sfnw-dev-owner/process-manuals/post-tilt-up/roof-framing-cklist.md

---
no-title-page: true
---

`#align(center,block[#set text(size:32pt); Post-Tilt-Up Checklist])`{=typst}

`#set text(size: 24pt);#v(3em)`{=typst}

- Attach White-Boards at Peak of Roof

- Align Rafters to Magic Studs

- Install Magic Stud Lag Bolts

- Secure Brackets at Peak of Roof

- Install Remaining Lag Bolts

- Install Bird Blocking

- Install Ridge Vent Blocks
