sfnw-dev-owner/process-manuals/Cut_Lists/Insulation.md

---
no-title-page: true
---

# INSULATION CUT LIST

## INTERIOR INSULATION

Cut and load in this order, back to front of the insulation cart, bottom level.

| Quantity | Dimensions | Notes |
| --- | --- | :--- |
| 12 | 24"x84" | Mark "Side Wall" |
| 2 | 24"x42" | Mark "Under Window" (2 pieces from one bat) |
| 1 | 24"x84" | Mark "Back Wall" |
| 1 | 24"x67½" | Mark "Under A/C" |
| 2 | 15½"x84" | Mark "Skinny" |

## EXTERIOR INSULATION

Cut and load in this order, back to front of the insulation cart, top level.

| Quantity | Dimensions | Notes |
| --- | --- | :--- |
| 8 | 24"x45½" | Mark "Middle Roof" (2 pieces from one bat) |
| 4 | 18"x45½" | Mark "End Roof" (2 pieces from one bat) |

Save some of the 12" cutoff pieces for use as insulation for
structural triangles; small pieces should be put into trash. There is a
black plastic bag for the saved insulation, next to the insulation
storage area.
