sfnw-dev-owner/process-manuals/Platform/Platform_sngl_side.md

```{=typst}
#title-page[
  #text(36pt, weight: "bold")[Platform]
  #v(1em)
  #text(24pt)[Jig Instructions]
]
```
# PLATFORM - SET UP LIST
- Put construction adhesive (Liquid Nails) by heater
- Caulking gun
- Framing nail gun
- Framing nails
- Screw gun with T25 bit
- Screws --- 3" with T25 head
- Screws --- hex head for brackets
- Brackets
- Chalk line
- Mallet
- Great Stuff cans
- 12" spacer blocks marked "SAVE"
- Jenga blocks

`#pagebreak()`{=typst}

# Step 1

- Set 2x6s into the jig to form the perimeter. Check the long 2x6s for straightness. If not straight, be sure to place them so that the curve
is inward at the center of each board. Put 1 FRAMING nail in each of the corners
    - one person holds flush on top and sides, other person nails
- Check the frame for square: measure the diagonals; they should be the same. Adjust as necessary.
- Put 2 more nails (total of 3) in a vertical line at each of the 4 corners.

`#pagebreak(); #fullpage("images/platform_01.pdf")`{=typst}

# Step 2
- Put a second 2x6 inside the ones on each short end
    - CLAMP them together
    - nail these 2x6 together 4 places at each end of frame, centered vertically
- Team leader
    - using the triangle, mark a line on the outside of the long 2x6s at the middle of the ends of each joist to show where the nails go.

`#pagebreak(); #fullpage("images/platform_02.pdf")`{=typst}

# Step 3
- Put in all the inner 2x6 joists
- Put 3 nails in a vertical line on each end of each joist
    - make sure joists are flush with side rail before nailing

`#pagebreak(); #fullpage("images/platform_03.pdf")`{=typst}

# Step 4

- Put pre-cut skids into the steel building carriages
    - longer part of the angled edges up
    - position each 4x6 skid so that the vertical mark on the skid lines up with the front of each carriage at the eventual front of the home.
- Install the alignment jigs, first to the front of the skids, and then to the back.
    - At the front, the cross bar should stick up above the tops of the  skids, and the two alignment blocks should be flush with the skid tops.
    - The skids should both be between the two alignment blocks.
- Place chocks under the wheels of one carriage, to keep if from moving.
- Measure diagonally from jig corner to corner and adjust the other carriage so that the jig is square.  Place chocks under its wheels.
- Pry the frame out of the framing jig, and lift the frame onto the pre-cut skids
    - At the front, the frame should be up against the alignment jig crossbar. At all four corners, the frame should fit into the metal angles.
    - Verify that the skids do not stick out beyond the back of the frame. If they do, they were not trimmed correctly, and this must be corrected.
- Measure the diagonals of the frame, and make sure that they are the same, so that the frame is square.
    - After any adjustments, **make sure** the frame is tight against the front jig crossbar.

`#pagebreak(); #fullpage("images/platform_04.pdf")`{=typst}

# Step 5

- Team Leader
    - make an X where the metal brackets should go
    - FOLLOW LOCATIONS on DIAGRAM
    - alternate inside of the skid and outside of the skid all the way to the rear
    - make sure to make a mark on the inside of the double joist at the rear.

`#pagebreak(); #fullpage("images/platform_05.pdf")`{=typst}

# Step 6
- At each X, screw in a metal bracket
    - use 6 small hexagonal screws for each metal bracket
    - 3 on the bottom 3 on the top, attaching the frame to the skids

`#pagebreak(); #fullpage("images/platform_06.pdf")`{=typst}

# Step 7

- Place blocks labeled "SAVE" in each bay, except the front and back bays
    - on top of each skid, centered between the joists.
    - DO NOT NAIL
    - In the front and back bays, place the "SAVE END" blocks

`#pagebreak(); #fullpage("images/platform_07.pdf")`{=typst}

# Step 8

- Put rigid insulation foam pieces into each bay
    - Cut the foam if not pre-cut. Use templates
    - 2 at 11^1^/~2~ inches wide by 92^1^/~2~ long
    - 7 at 14 inches wide by 92^1^/~2~ long
    - use an Exacto knife with blade all the way out
    - Cut the ends to fit the length, and install with silver side UP.
- Using GREAT STUFF spray cans
    - put lines to fill in at all the junctions between the foam and the joists.
    - Start with tip of spray can at the middle, and pull towards you.
    - DO NOT SET THE SPRAY CANS ON WORK STATIONS

`#pagebreak(); #fullpage("images/platform_08.pdf")`{=typst}

# Step 9
- Under the 1^st^ plywood panel ONLY
    - put Liquid Nails construction adhesive on each of the joists and along the side rails, only along the first 3 bays. 
- Place the 1^st^ plywood panel (3/4" CDX plywood)
    - use panels from pile labeled PLATFORM
    - line it up to be flush with the outer edges and the middle of the inner joist.
- Put a nail in that inner joist corner. Use that as the pivot point to line up the panel
- Nail about 8 inches apart along 2 edges using 3" framing nails.
- Put a chalk line at the intermediate joists
    - get up on platform and closely straddle the chalk line (joist) to push the plywood board down while nailing
    - walk backwards while nailing 8 inches apart.
- Nail along all chalk lines in a pattern going diagonally towards the opposite corner from where you started

`#pagebreak(); #fullpage("images/platform_09.pdf")`{=typst}

# Step 10

- Apply Liquid Nails construction adhesive to the joists that will be under the 2^nd^ plywood panel
- Place the 2^nd^ panel
    - at one side of the platform, put one nail into the 2^nd^ panel at the corner close to the 1^st^ panel
    - use this pivot point at the junction of the 2 panels to align the 2^nd^ panel
    - along the seam, nail about every 8 inches, slightly angled in towards the junction line
- Nail along edges and chalk lines

`#pagebreak(); #fullpage("images/platform_10.pdf")`{=typst}

# Step 11

- Apply Liquid Nails construction adhesive to the joists that will be under the 3^rd^ plywood panel
- Place the 3^rd^ panel
    - at one side of the platform, put one nail into the 3^rd^ panel at the corner close to the 2^nd^ panel
    - use pivot point at the junction of these panels to align the 3^rd^ panel
    - along the seam, nail about every 8 inches, slightly angled in towards the junction line
- Nail along edges and chalk lines

`#pagebreak(); #fullpage("images/platform_11.pdf")`{=typst}

# Step 12

- Router the edges of the platform. Ideally this would be done the next day, to let the liquid nails dry, but if tilt-up will be happening same-day, do it now.
  - Wipe off any liquid nails that's been squeezed out around the platform's perimeter.
  - Router the edges.
  - Clean the router's blade & table using an exacto knife and paper towel / rag. Try to leave all of the knife, router blade, and router table free of adhesive.

- Draw a line 3½ inches from the edge on all sides
    - use the marking jig; it hangs from the back saw table. Using a felt-tip pen, hold it against the inside of the jig,
    and slide the jig along the sides of the platform.

`#pagebreak(); #fullpage("images/platform_12.pdf")`{=typst}
