sfnw-dev-owner/process-manuals/Cut_Lists/Interior_Trim_Items.md

---
no-title-page: true
---

# Interior Trim Pick List

## Trim Racks -- West Wall

Trim widths (4" or 2") are approximate.  Do not rely on these dimensions.

| Qty | Size | Length | Description |
| :--- | :--- | :--- | --- |
|  3 | 3/4 x 4 | 12 ft | PVC Baseboards |
| 16 | 1/2 x 2 | 96" | Long Trim |
|  6 | 1/2 x 2 | 44" or 48"| Short Trim |
|  5 | 1/2 x 2 | 38" | Window Opening Trim |
|  6 | 1/2 x 3-1/8 | 35" | Window Liner |
|  6 | 1/2 x 2 | 42" | Ceiling Seam Trim |
|  2 | 1/2 x 2 | 42" | Triangle Trim -- Left |
|  2 | 1/2 x 2 | 42" | Triangle Trim -- Right |
|  2 | 1/2 x 2 | 12" | Triangle Trim -- Center  (use scraps)|
|  1 | 1/2 x 9-1/2| 96" | Wide Trim -- Front Door |

## Window Shelves -- near Band Saw

| Qty | Size | Length | Description |
| :--- | :--- | :--- | --- |
| 1 | 3/4 x 8 | 40" | Rear Shelf |
| 1 | 3/4 x 8 | 40" | Front Shelf |
| 1 | 2 x 4 | 39" | Rear Support Block |
| 1 | 2 x 4 | 39-1/2" | Front Support Block |

## Vent Cap (on Trim Rack)

| Qty | Size | Length | Description |
| :--- | :--- | :--- | --- |
| 1 | 1/2 x 9-1/2 | 96" | Wide Trim |
| 1 | 1/2 x 9-1/2 | ~44" | Wide Trim |
| 4 | 2 x 4 | 6-1/2" | Vent Block |

### Notes

- Verify width between finished window liner and midpoint of door frame, and rip 9-1/2 plank to this width.  Remaining strip can be used behind the door.
- Match plank widths of Wide Trim for Vent Cap, so that the seam will be less obvious
- Cut 13" blocks under front chop saw in half for Vent Blocks
