sfnw-dev-owner/process-manuals/Extract_Iron_Carts/images/01_Prepare.pdf

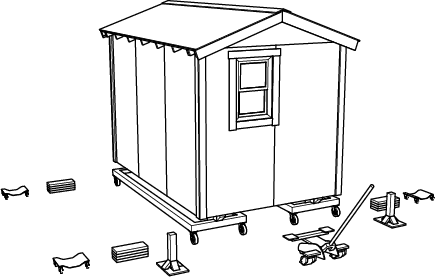
[picture p63: page 1]
