sfnw-dev-owner/process-manuals/Platform/archived/README.md

The files in this directory were used in Oct/Nov 2025 while building
for Eagle Village for Chief Seattle Club. They describe how to build a
platform with doubled side rails (2x6x12'), which we don't do anymore.
