sfnw-dev-owner/process-manuals/Platform/archived/images/platform_v2_01.pdf

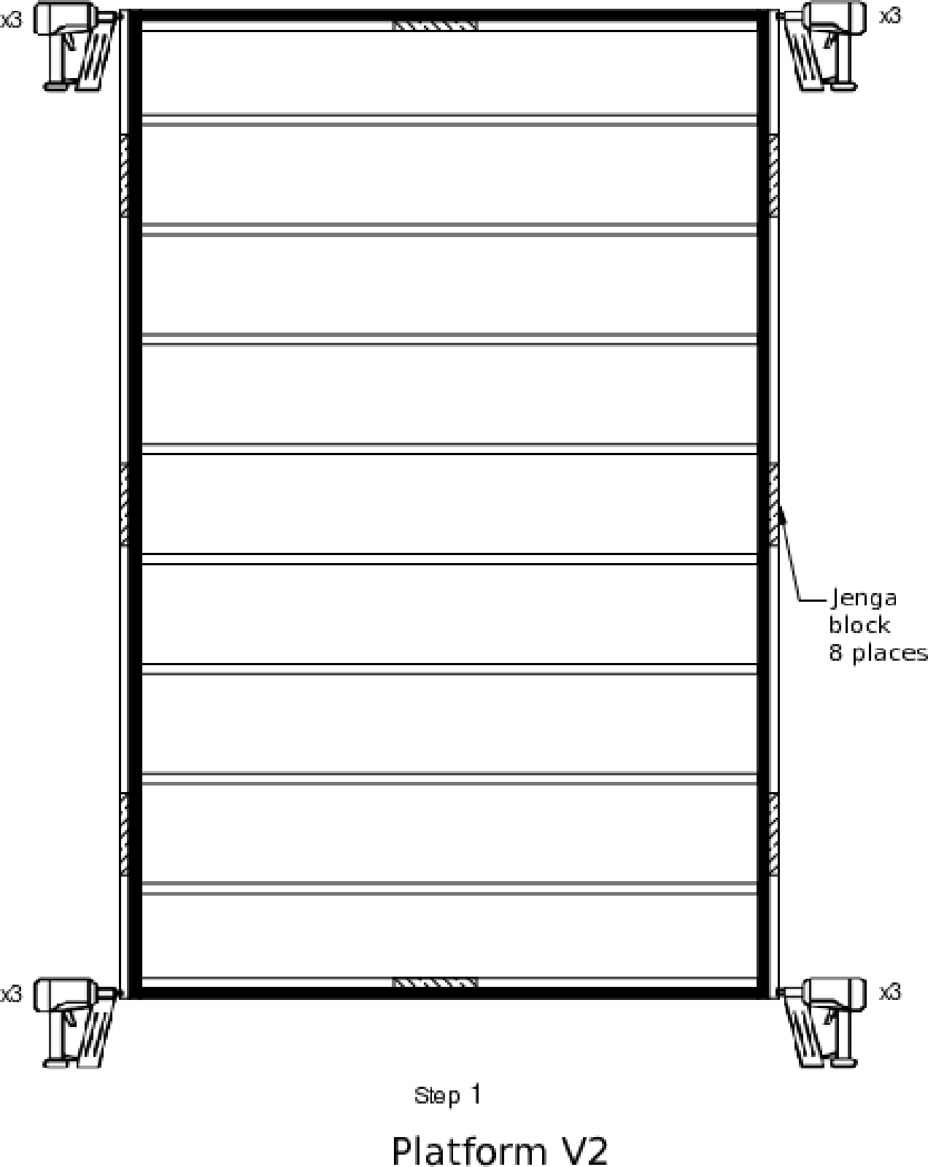
[picture p64: page 1]
