sfnw-dev-owner/process-manuals/Platform/archived/images/platform_v2_02.pdf

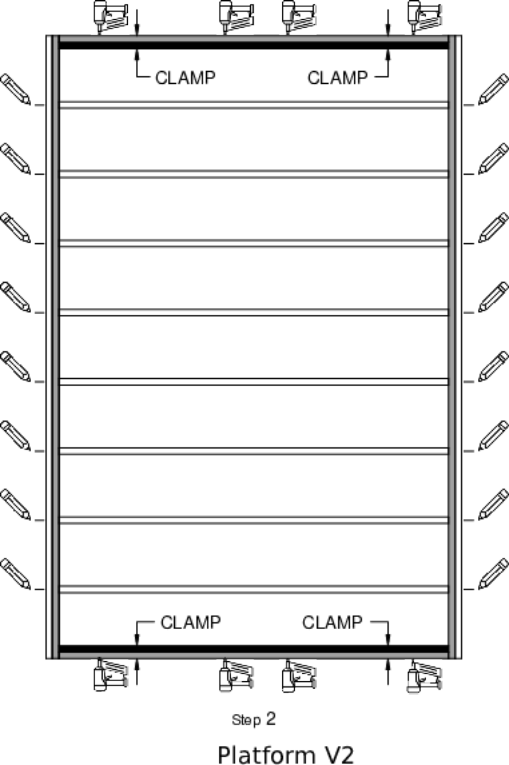
[picture p65: page 1]
