sfnw-dev-owner/process-manuals/Platform/archived/images/platform_v2_03.pdf

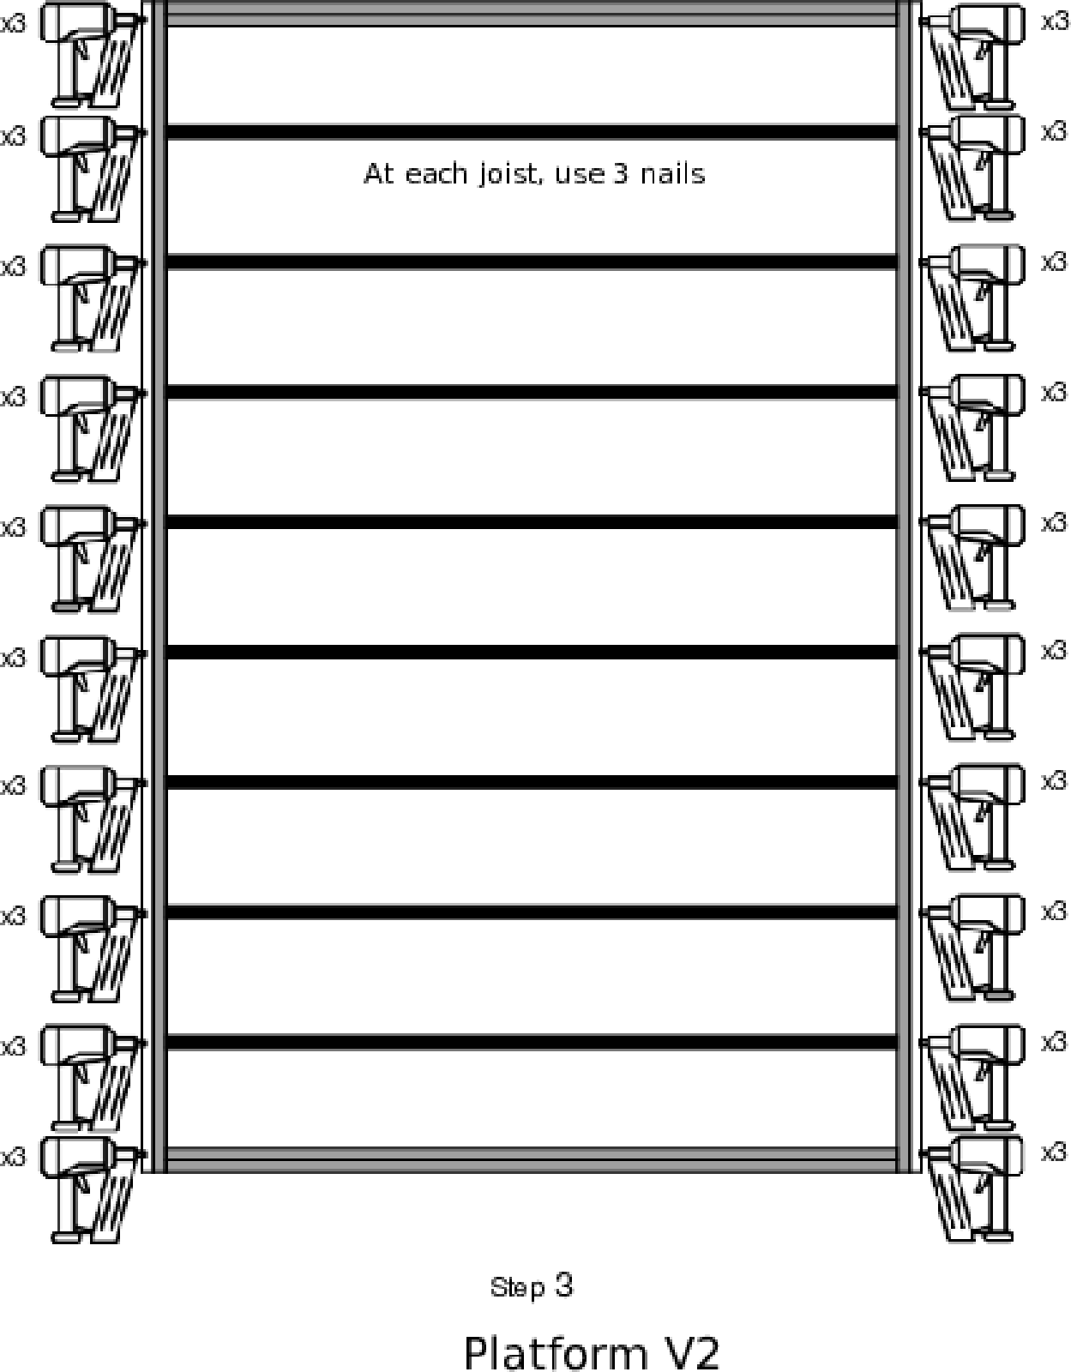
[picture p66: page 1]
