sfnw-dev-owner/process-manuals/Platform/archived/images/platform_v2_04.pdf

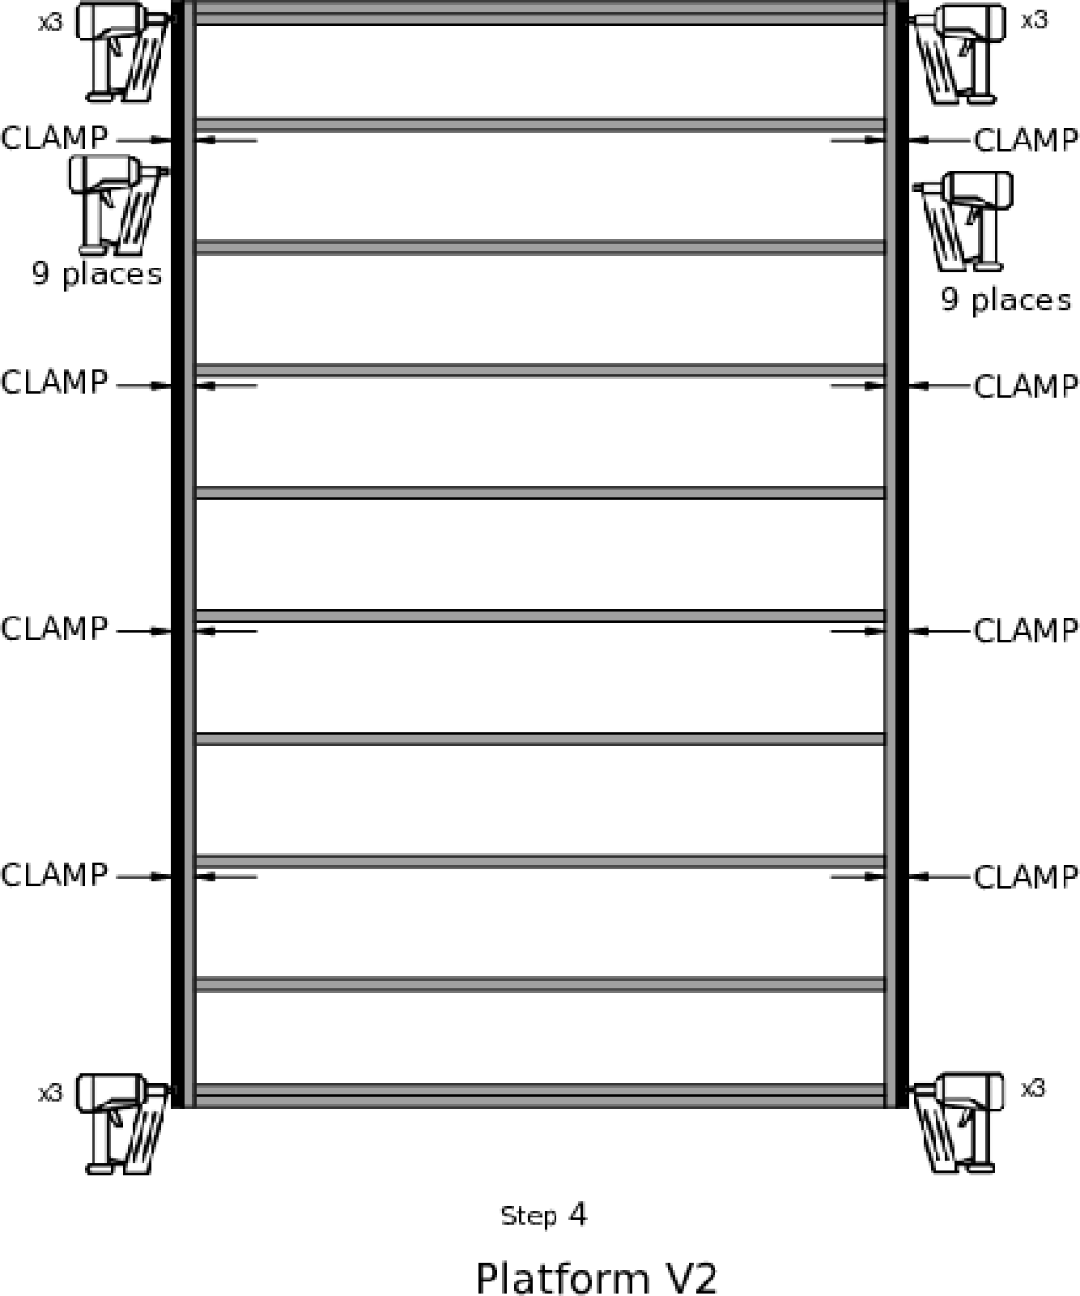
[picture p67: page 1]
