sfnw-dev-owner/process-manuals/Platform/archived/images/platform_v2_05.pdf

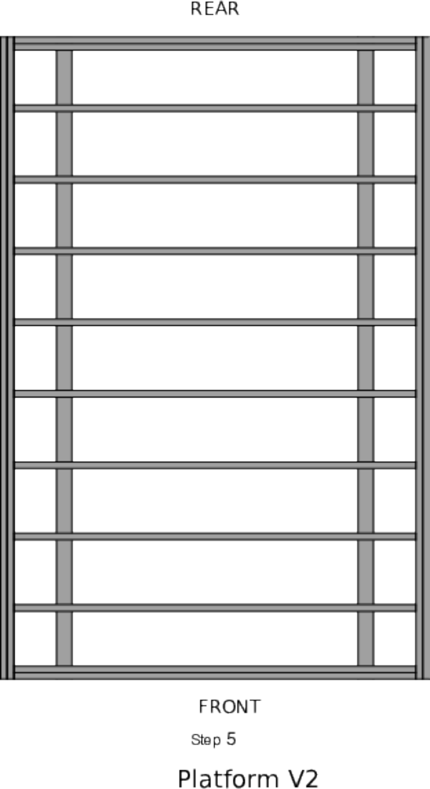
[picture p68: page 1]
