sfnw-dev-owner/process-manuals/Platform/archived/images/platform_v2_06.pdf

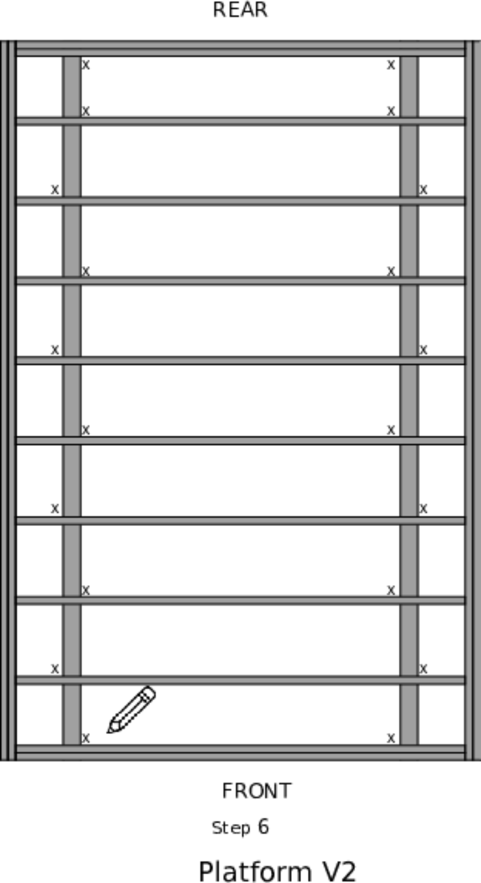
[picture p69: page 1]
