sfnw-dev-owner/process-manuals/Platform/archived/images/platform_v2_07.pdf

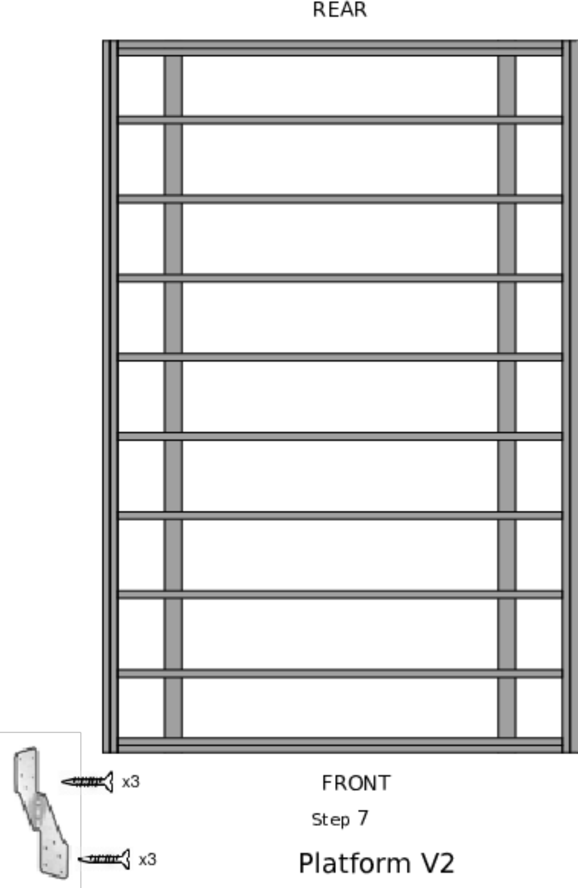
[picture p70: page 1]
