sfnw-dev-owner/process-manuals/Platform/archived/images/platform_v2_08.pdf

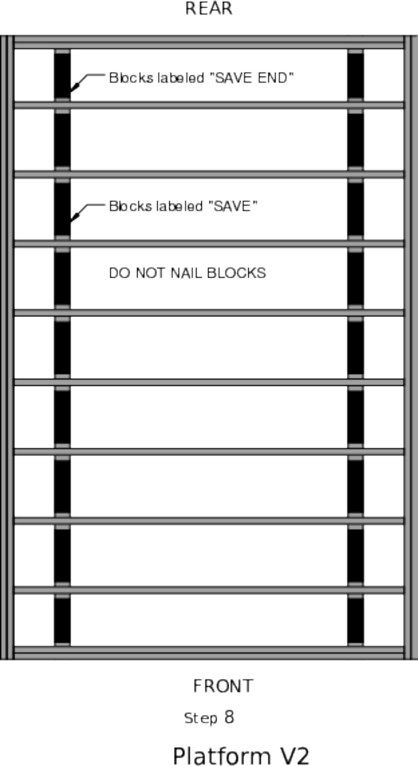
[picture p71: page 1]
