sfnw-dev-owner/process-manuals/Platform/archived/images/platform_v2_09.pdf

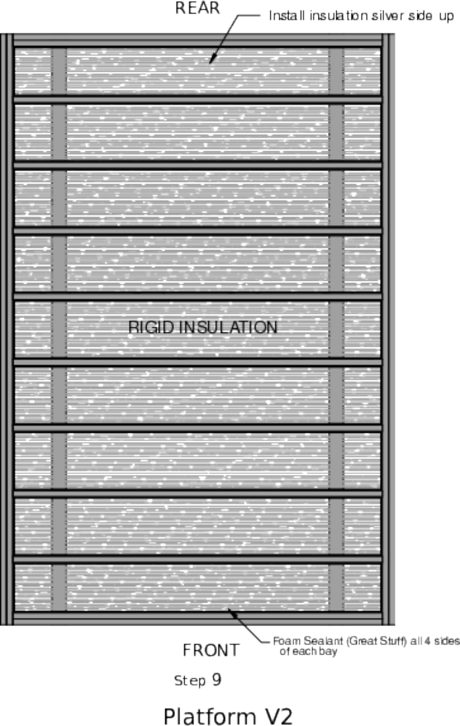
[picture p72: page 1]
