sfnw-dev-owner/process-manuals/Platform/archived/images/platform_v2_10.pdf

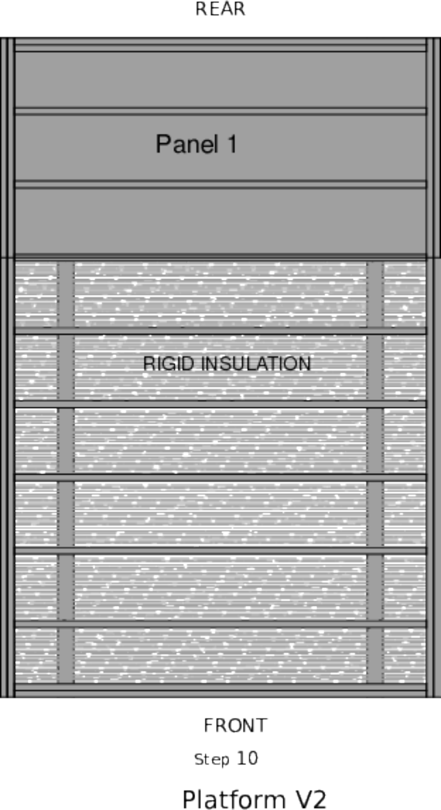
[picture p73: page 1]
