sfnw-dev-owner/process-manuals/Platform/archived/images/platform_v2_11.pdf

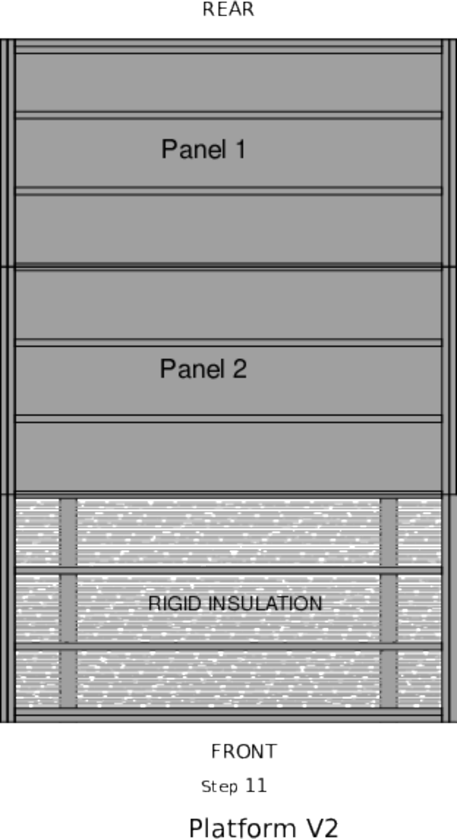
[picture p74: page 1]
