sfnw-dev-owner/process-manuals/Platform/archived/images/platform_v2_12.pdf

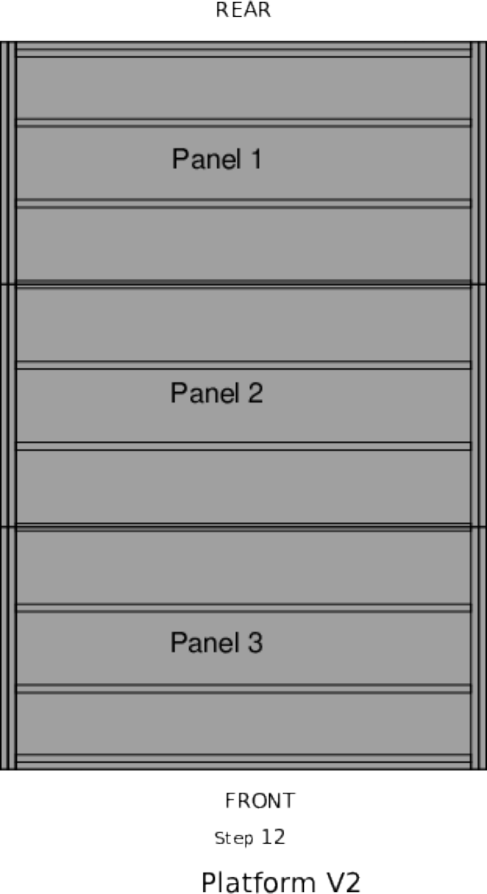
[picture p75: page 1]
