sfnw-dev-owner/process-manuals/Platform/archived/images/platform_v2_13.pdf

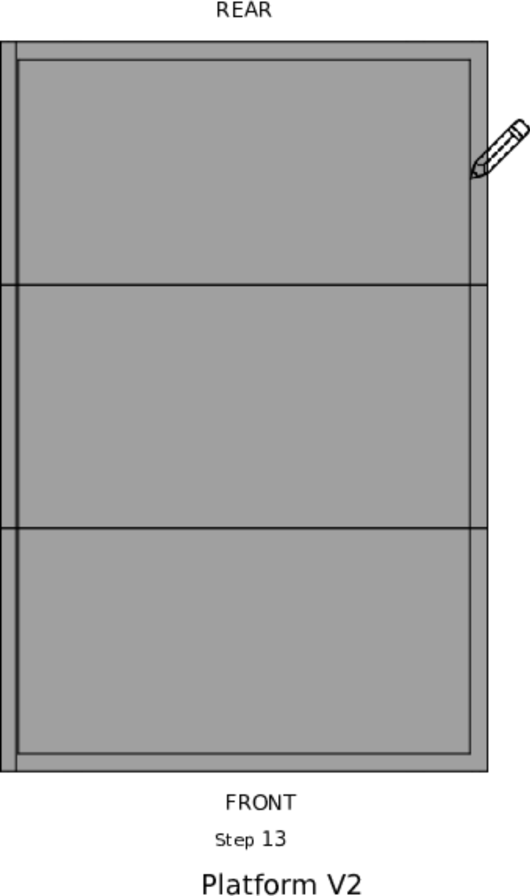
[picture p76: page 1]
