sfnw-dev-owner/process-manuals/post-tilt-up/images/image_44.png

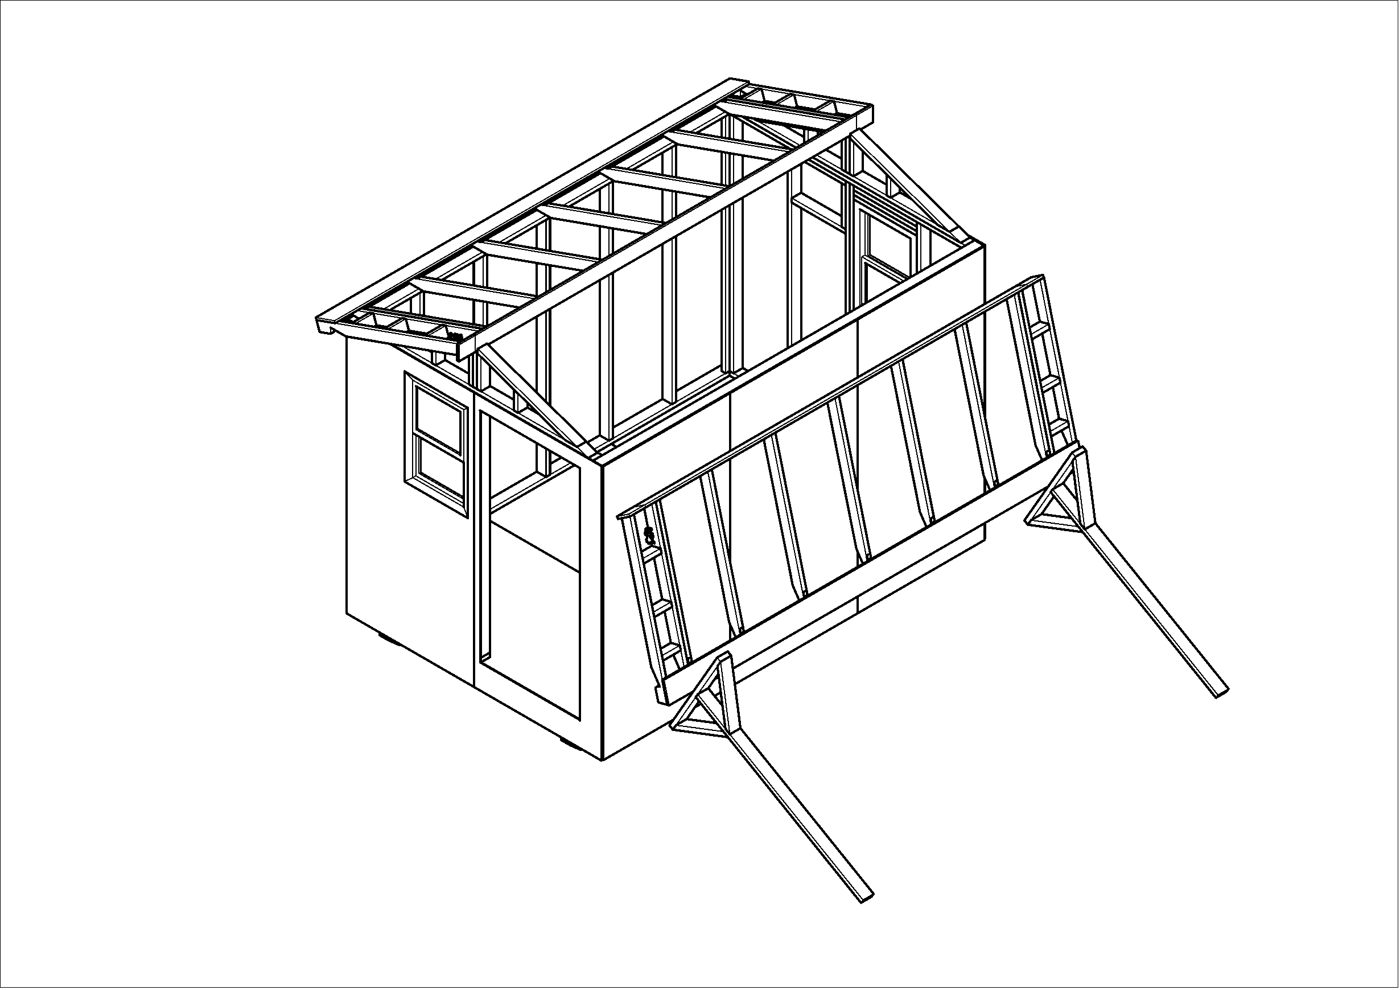
post-tilt-up/images/image_44.png
