sfnw-dev-owner/process-manuals/tilt-up/images/image_04.png

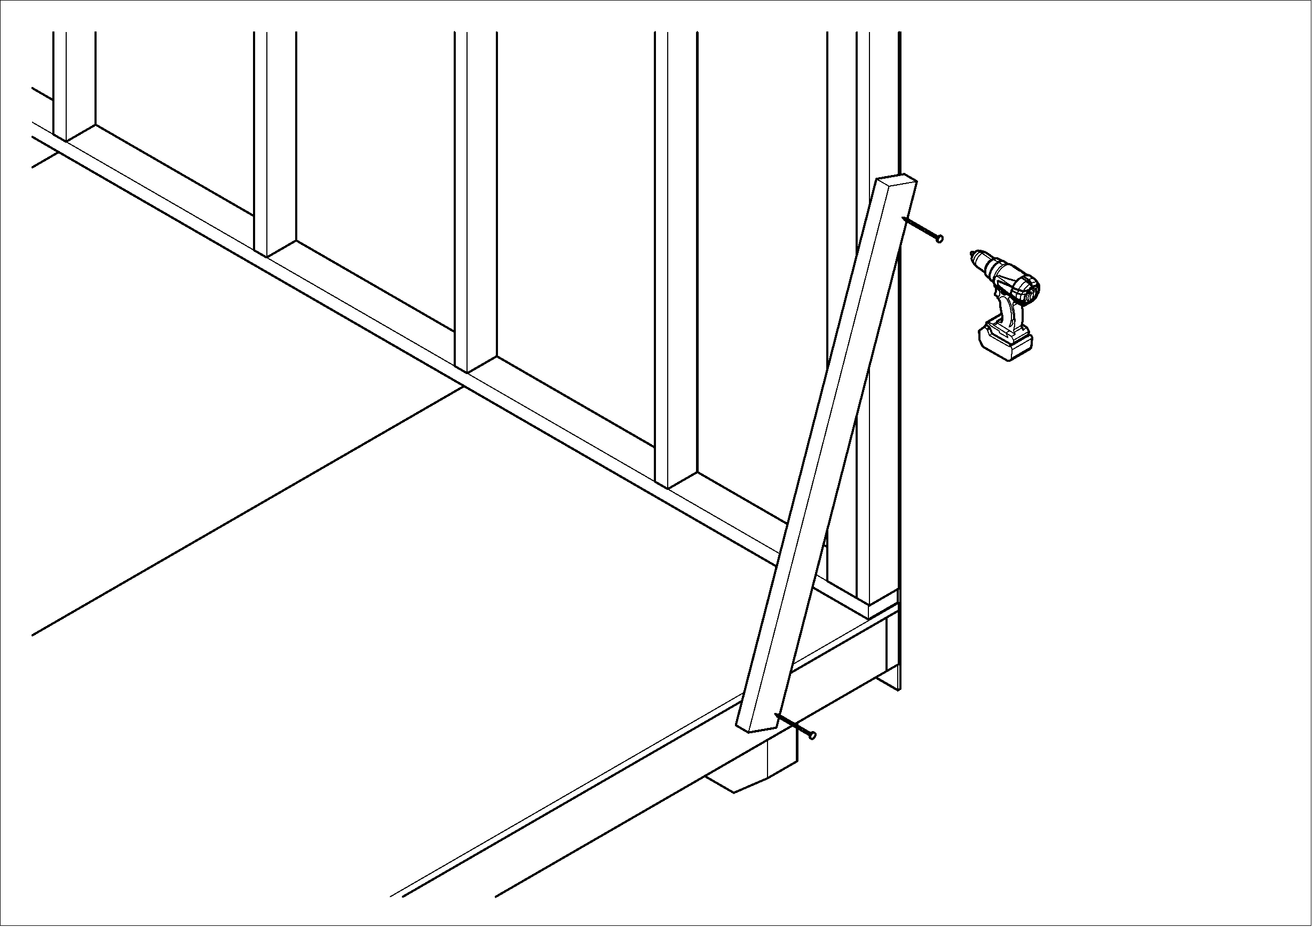
tilt-up/images/image_04.png
