sfnw-dev-owner/process-manuals/tilt-up/images/image_07.png

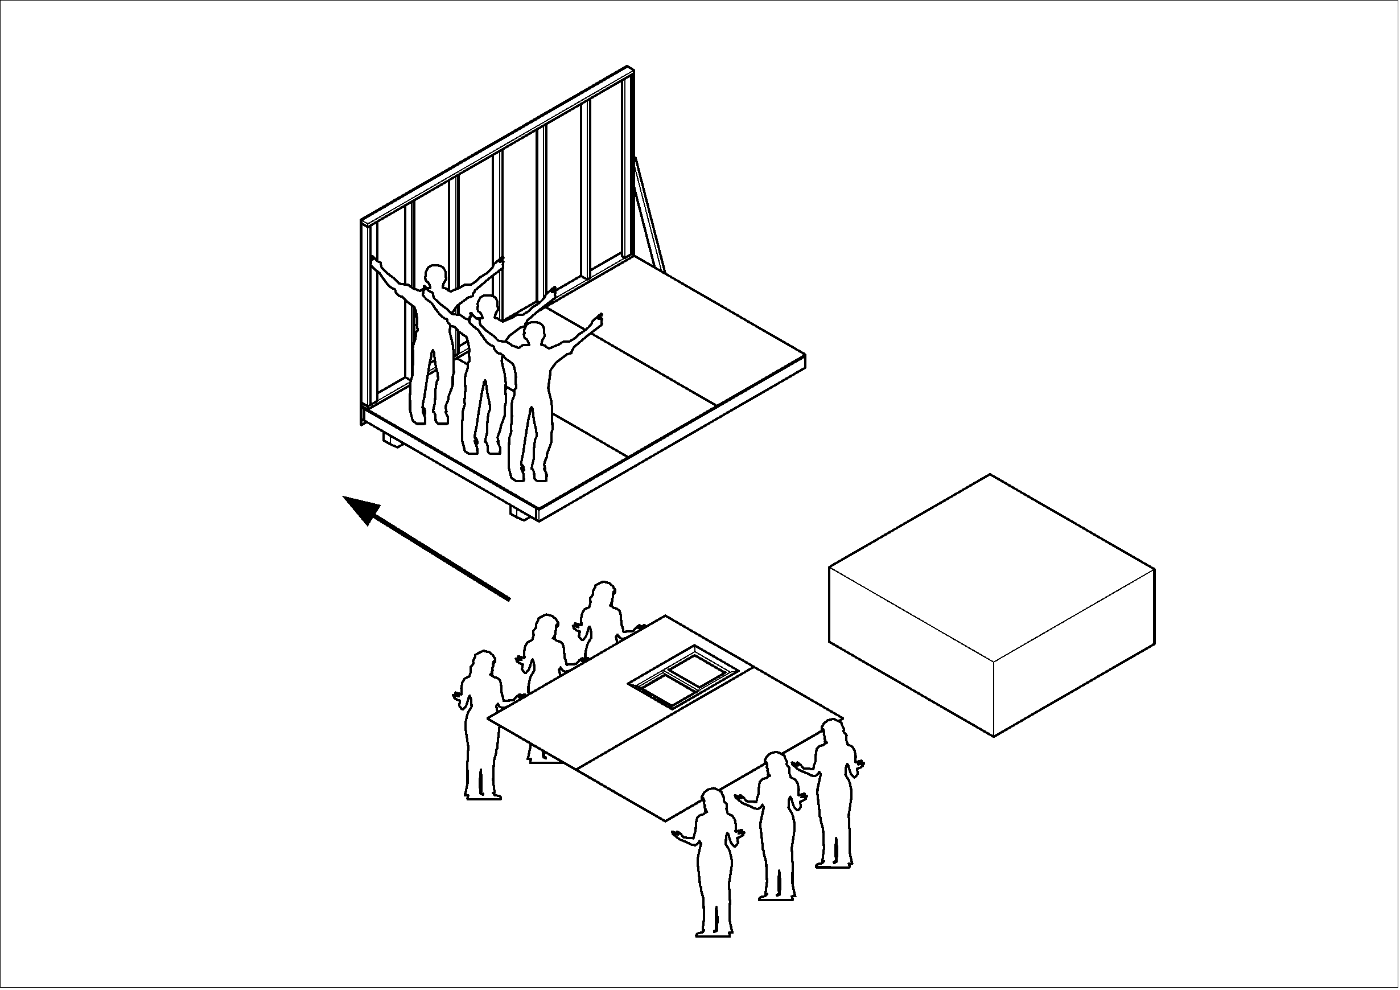
tilt-up/images/image_07.png
