sfnw-dev-owner/process-manuals/tilt-up/images/image_08.png

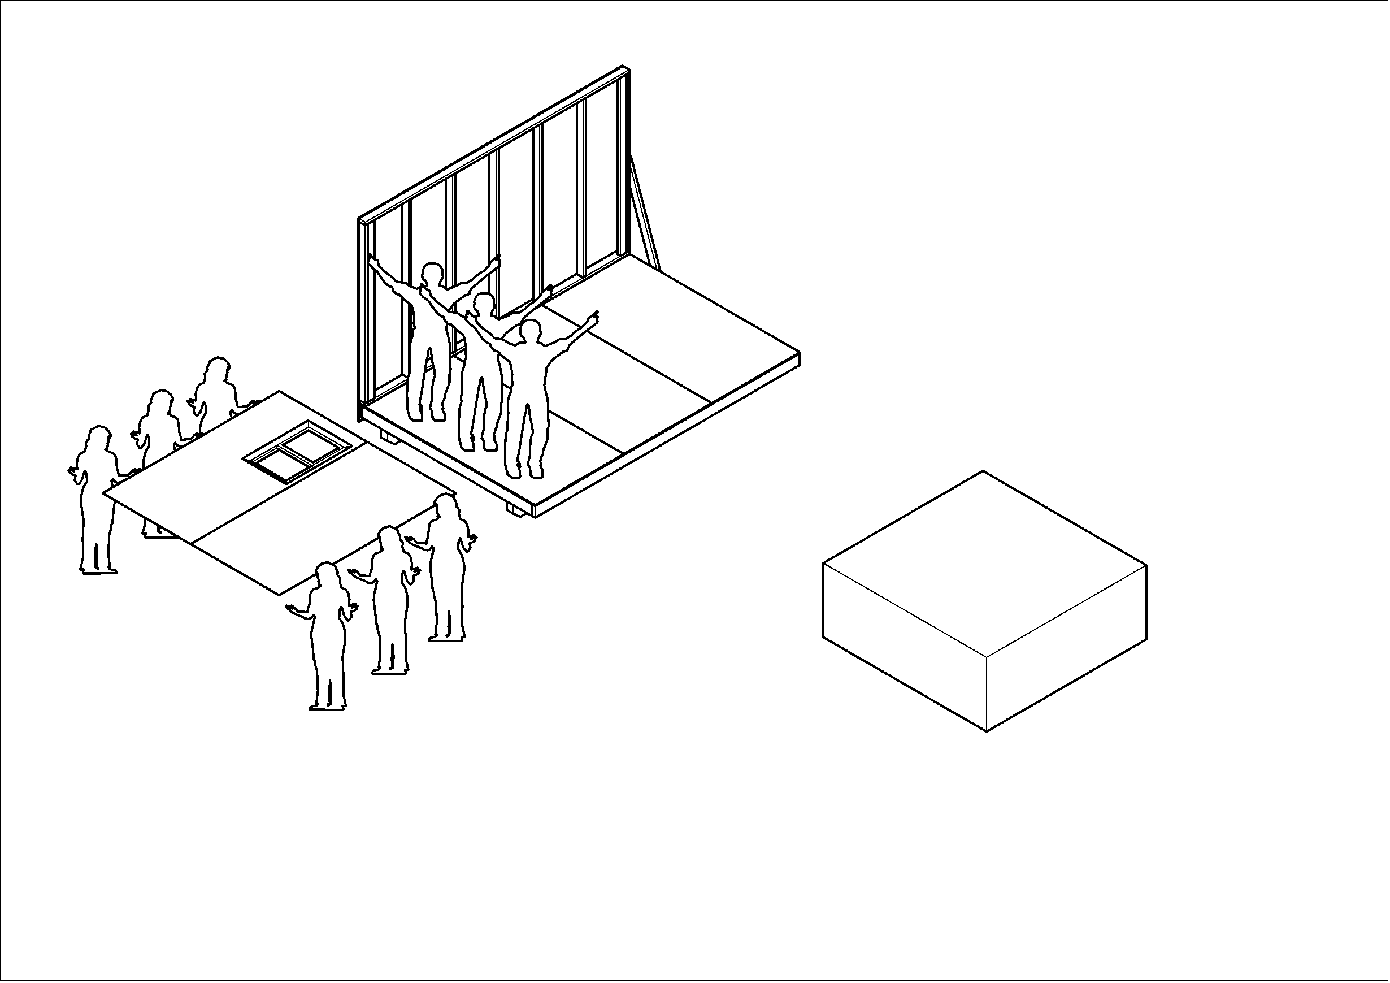
tilt-up/images/image_08.png
