sfnw-dev-owner/process-manuals/tilt-up/images/image_10.png

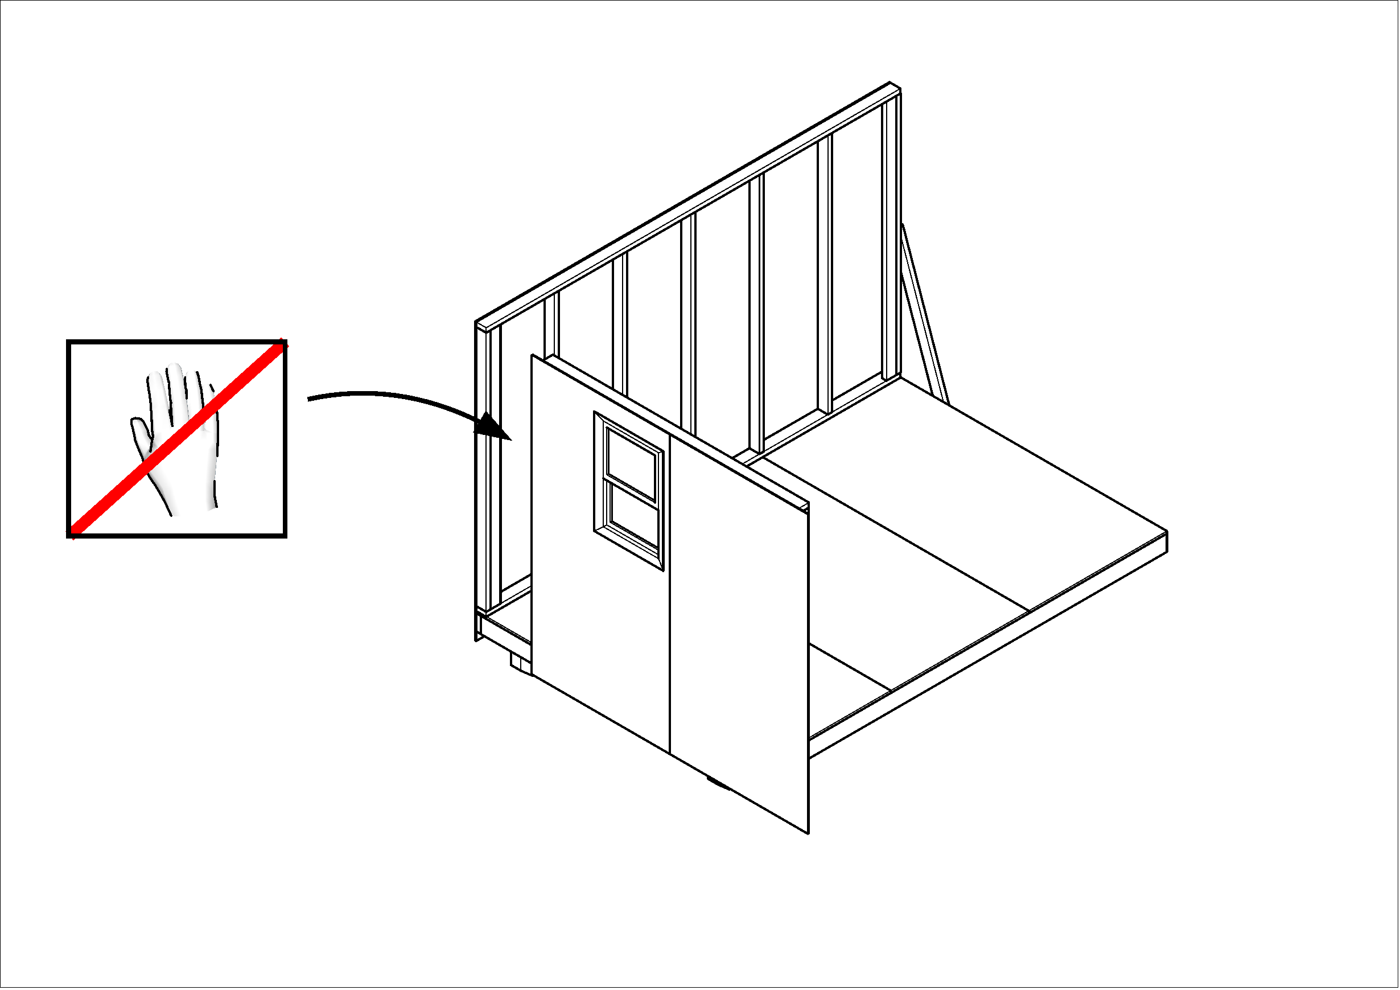
tilt-up/images/image_10.png
