sfnw-dev-owner/process-manuals/tilt-up/images/image_11.png

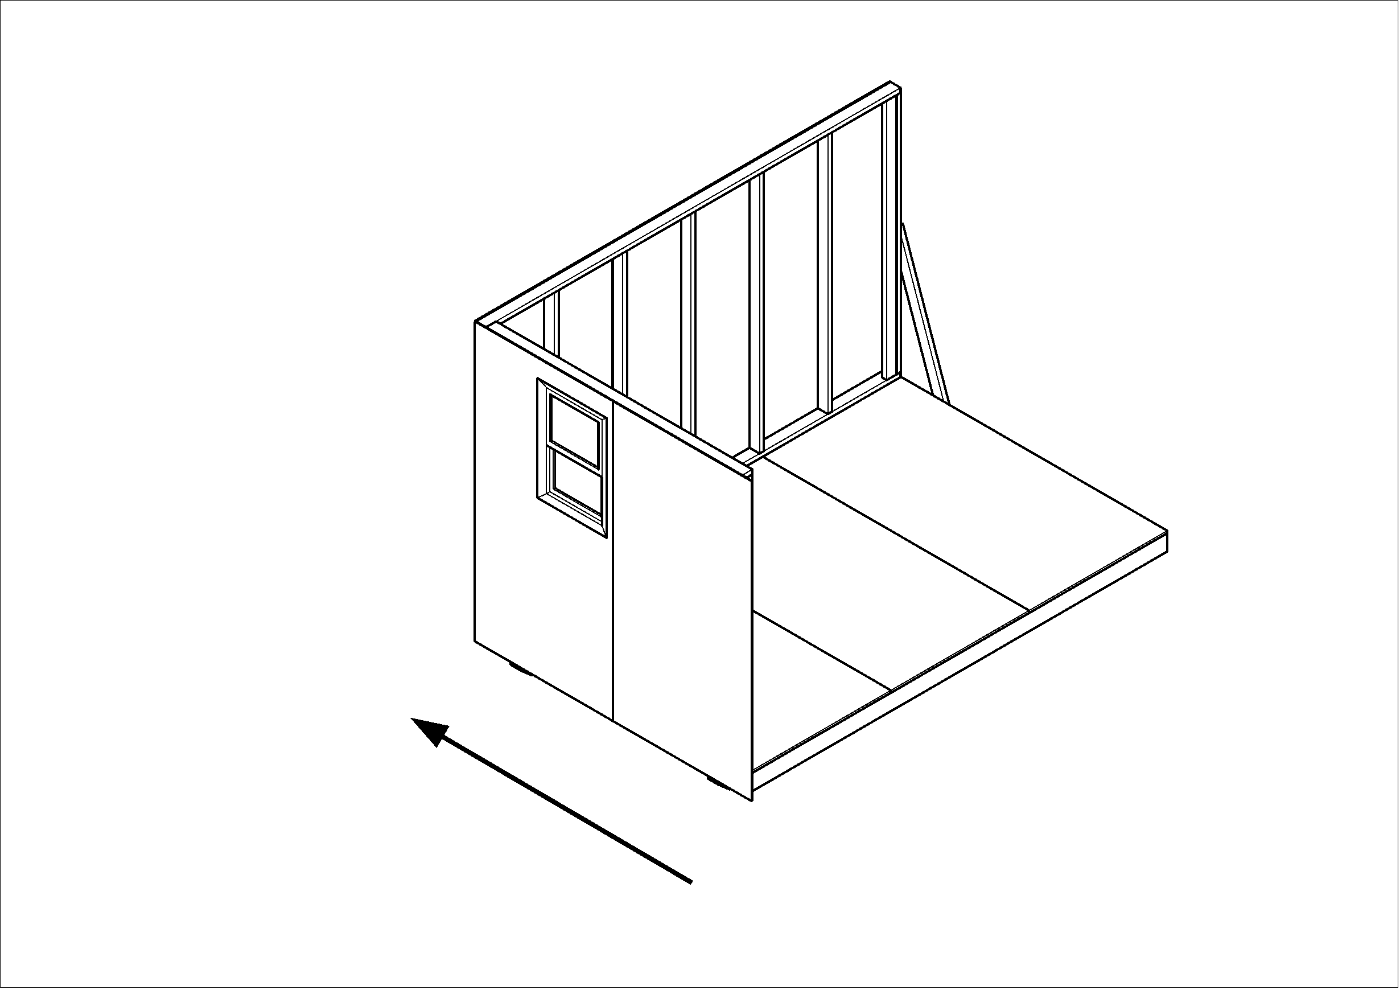
tilt-up/images/image_11.png
