sfnw-dev-owner/process-manuals/tilt-up/images/image_15.png

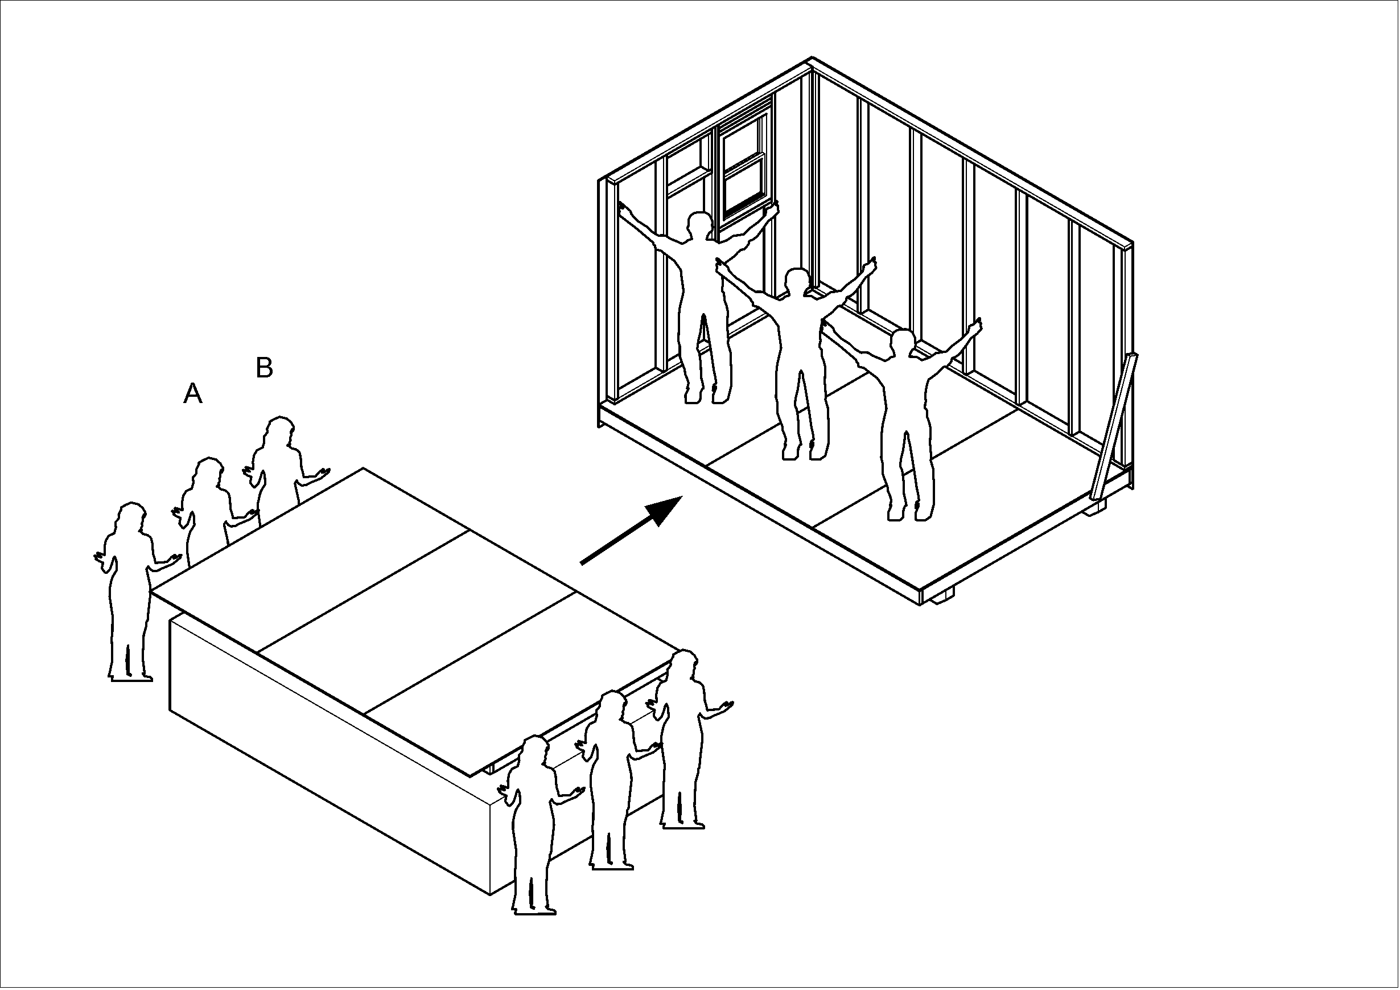
tilt-up/images/image_15.png
