sfnw-dev-owner/process-manuals/tilt-up/images/image_17.png

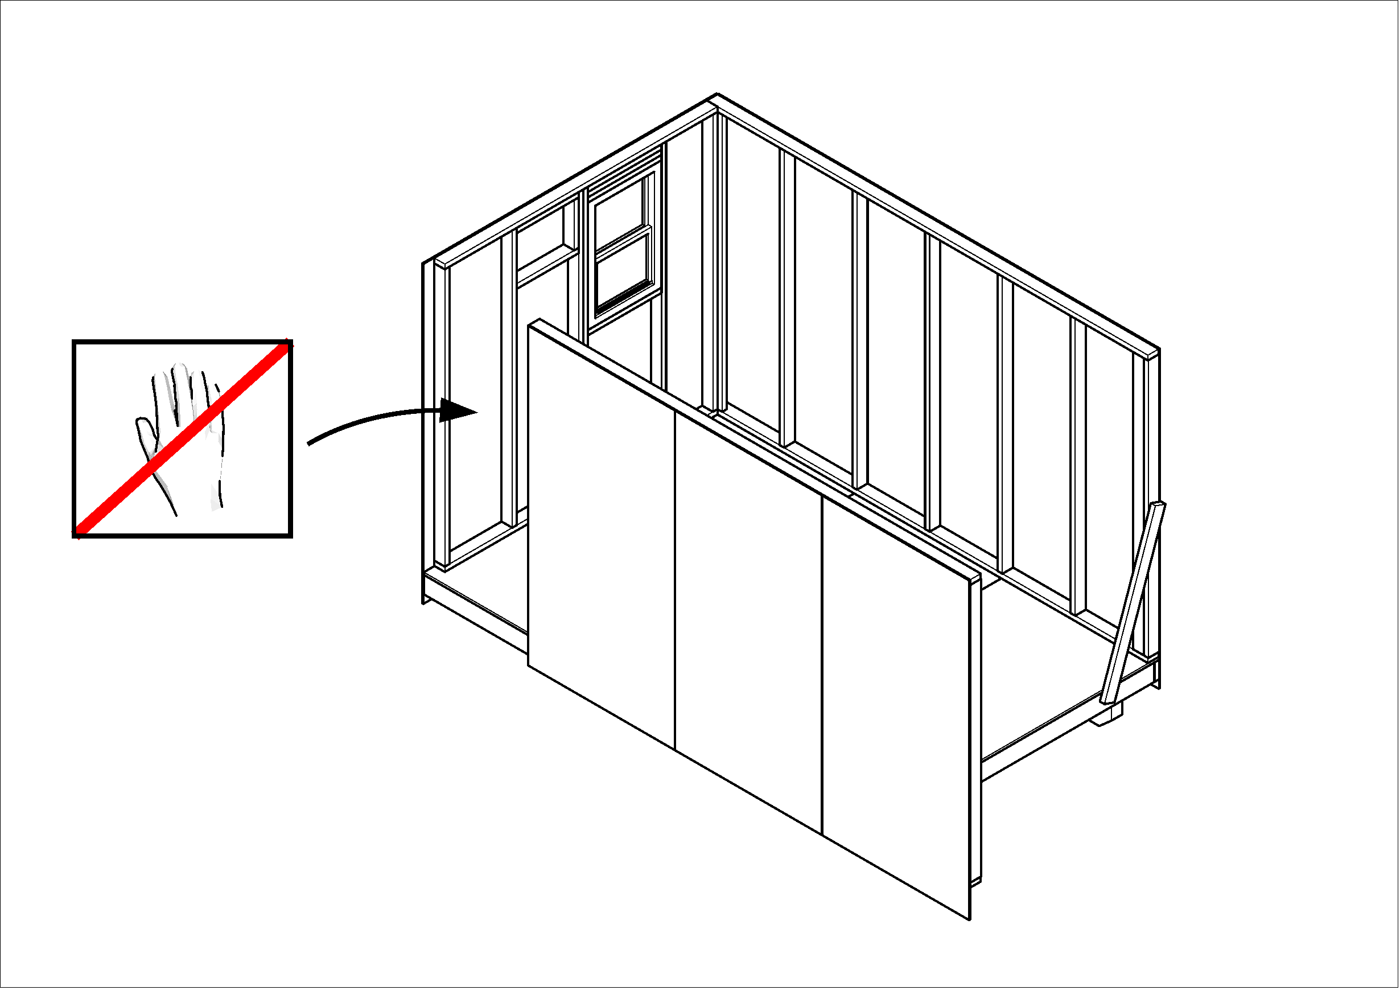
tilt-up/images/image_17.png
