sfnw-dev-owner/process-manuals/tilt-up/images/image_18.png

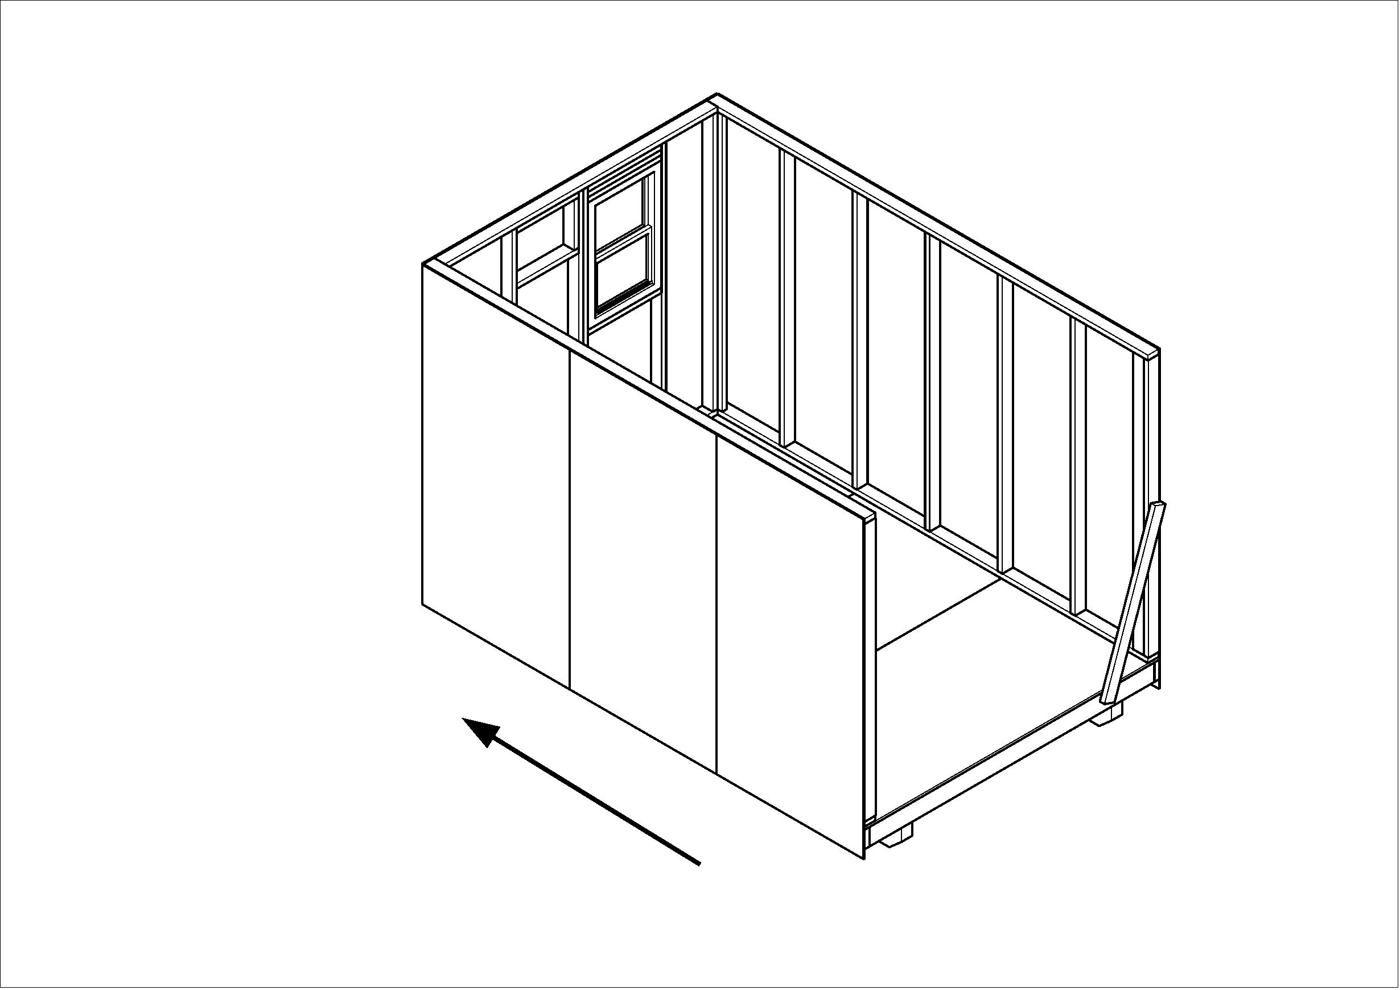
tilt-up/images/image_18.png
