sfnw-dev-owner/process-manuals/tilt-up/images/image_24.png

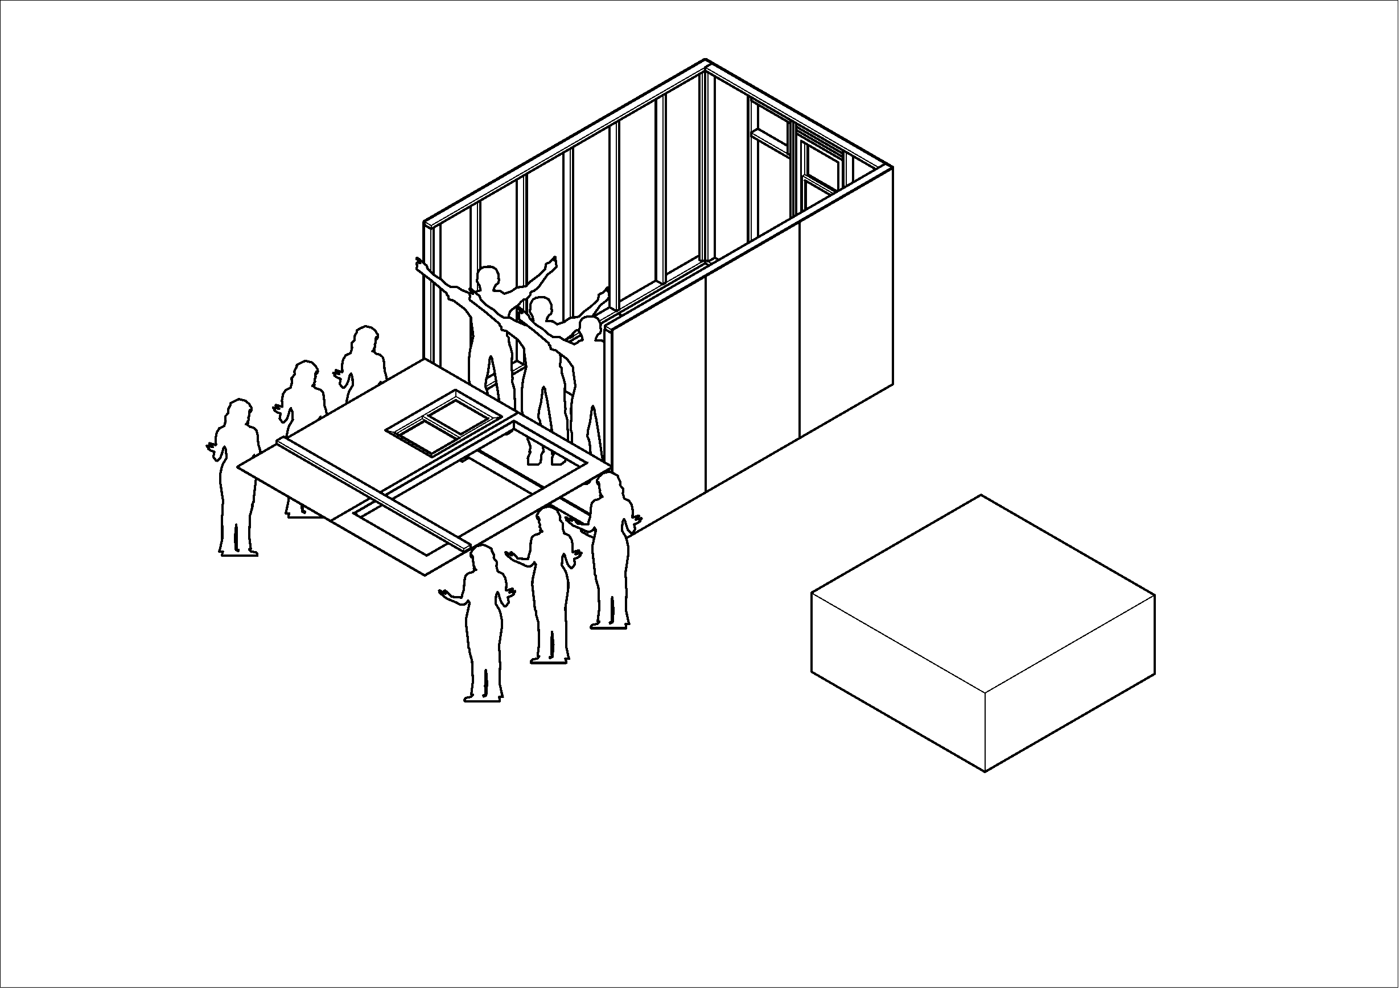
tilt-up/images/image_24.png
