sfnw-dev-owner/process-manuals/tilt-up/images/image_25.png

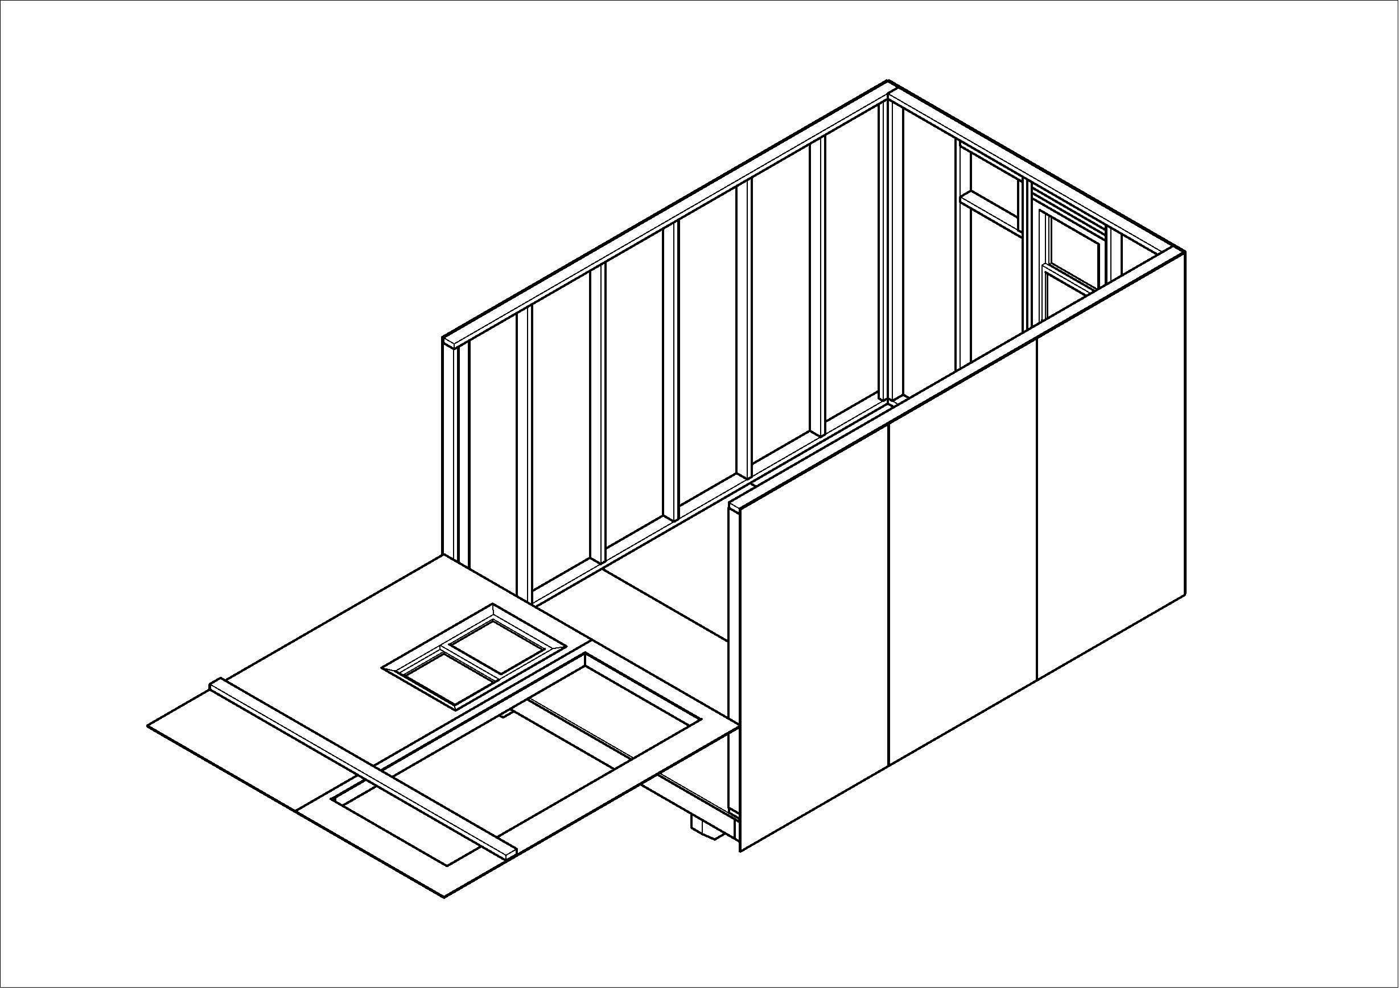
tilt-up/images/image_25.png
