sfnw-dev-owner/process-manuals/tilt-up/images/image_26.png

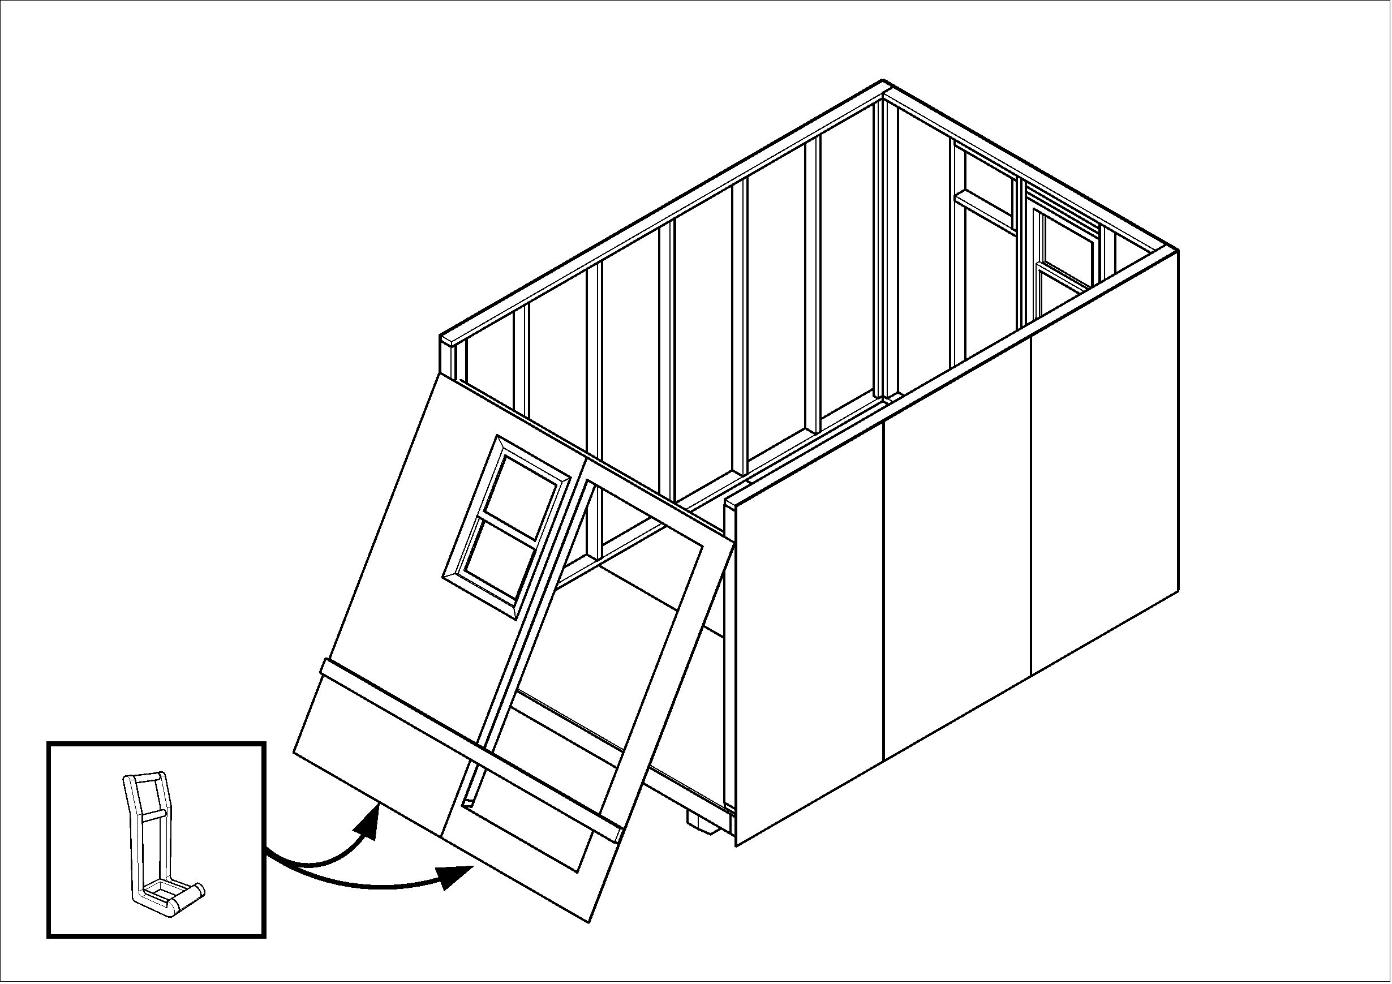
tilt-up/images/image_26.png
