sfnw-dev-owner/process-manuals/tilt-up/images/image_27.png

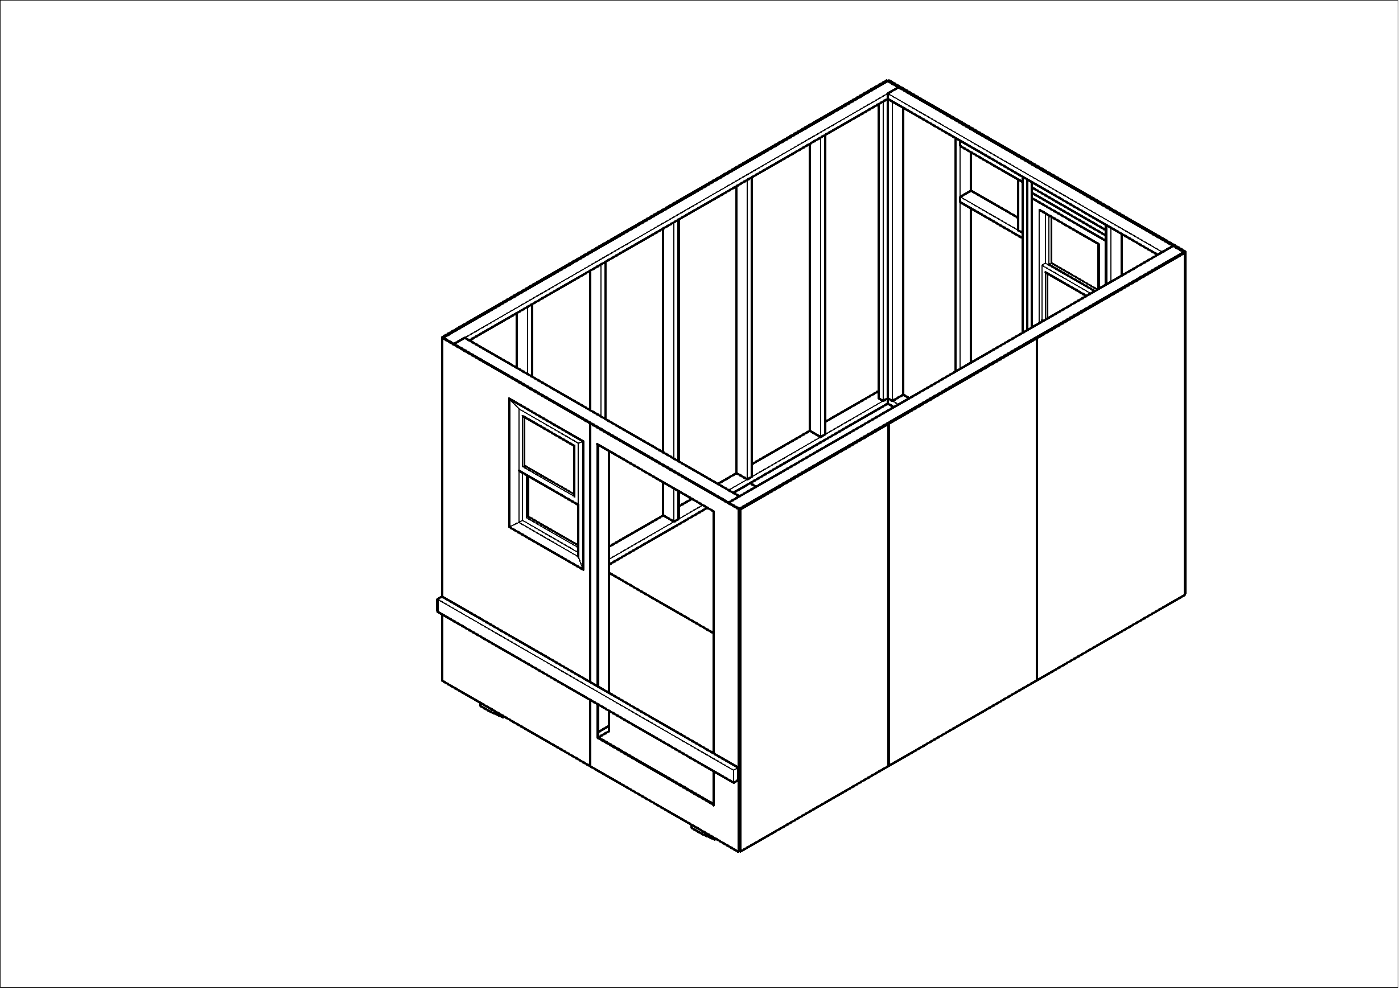
tilt-up/images/image_27.png
