sfnw-dev-owner/process-manuals/Interior_Trim/Images/front_window.dxf

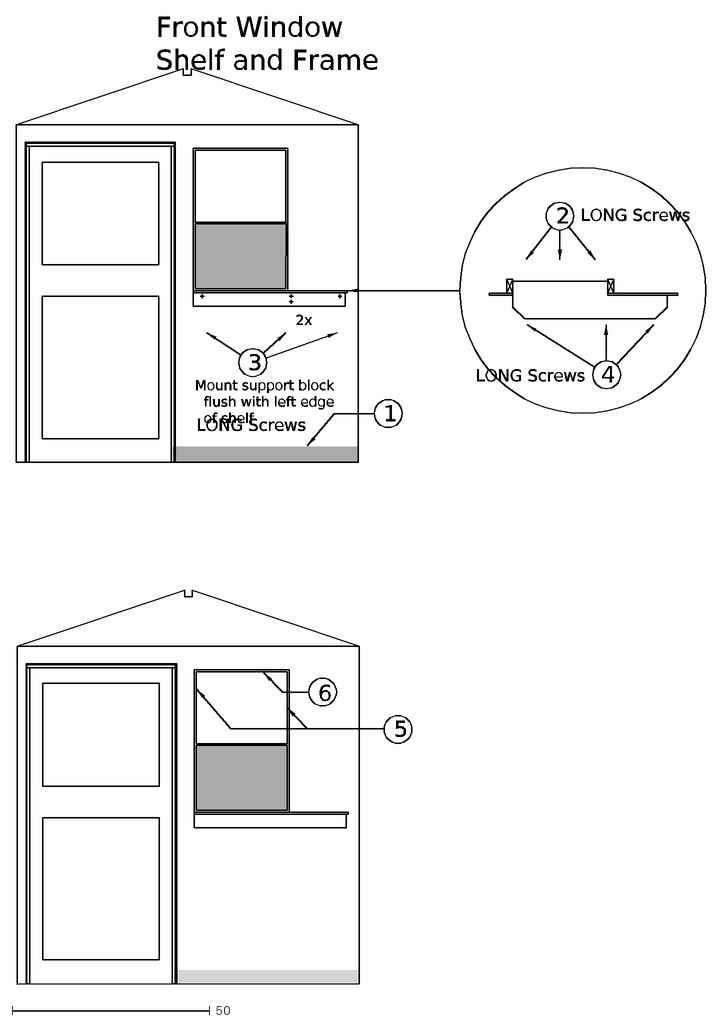
[picture p93: CAD file, 2026-09-18]
Interior_Trim/Images/front_window.dxf
2
3
1
4
5
6
2x
Mount support block flush with left edge of shelf
Front Window Shelf and Frame
LONG Screws
