sfnw-dev-owner/process-manuals/Interior_Trim/Images/combo_trim.dxf

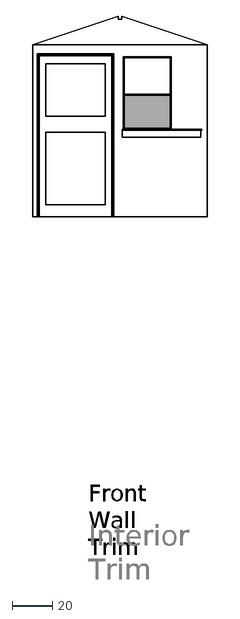
[picture p94: CAD file, 2026-08-30]
Interior_Trim/Images/combo_trim.dxf
Front Wall Trim
Interior Trim
